Justblanken17/ECEN404repo/Adam/Firmware/Carbon_Dioxide_Sensor/carbon_dioxide_sensor.h

/* 
 * File:   carbon_dioxide_sensor.h
 * Author: Adam Pameron
 *
 * Created on October 24, 2022, 3:00 PM
 */

#ifndef CARBON_DIOXIDE_SENSOR_H
#define	CARBON_DIOXIDE_SENSOR_H

#ifdef	__cplusplus
extern "C" {
#endif

float getCarbonDioxideData(void);


#ifdef	__cplusplus
}
#endif

#endif	/* CARBON_DIOXIDE_SENSOR_H */
